majster-pl/ship-it-button/images/quick_guide.png

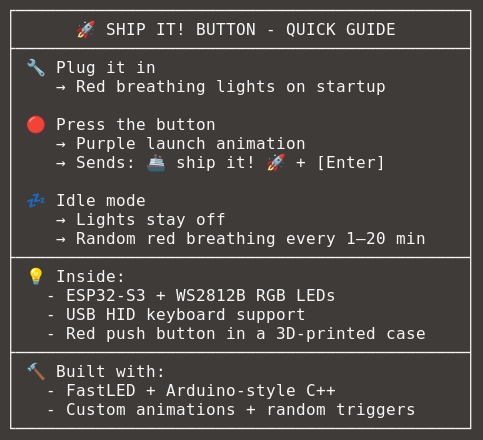
images/quick_guide.png
