majster-pl/ship-it-button/images/quick_guide_with_qr.png

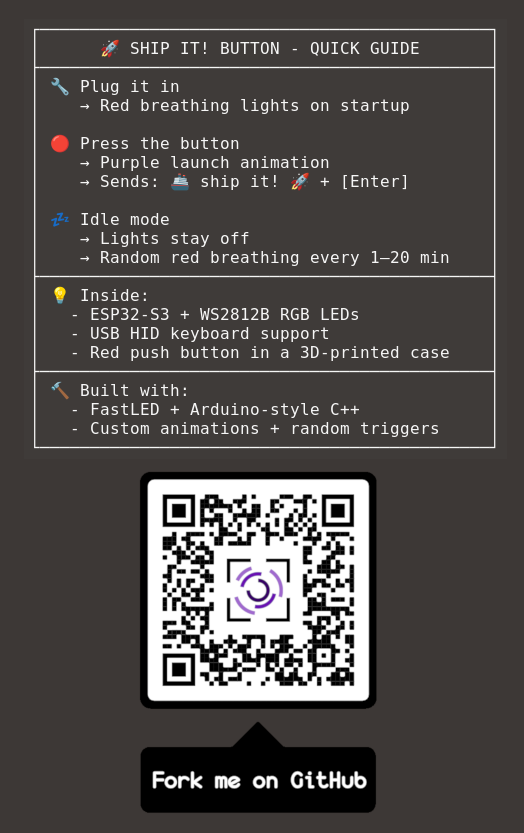
images/quick_guide_with_qr.png
